Kartoffel/BareDuino/Nano/pictures/IMG_1930.jpg

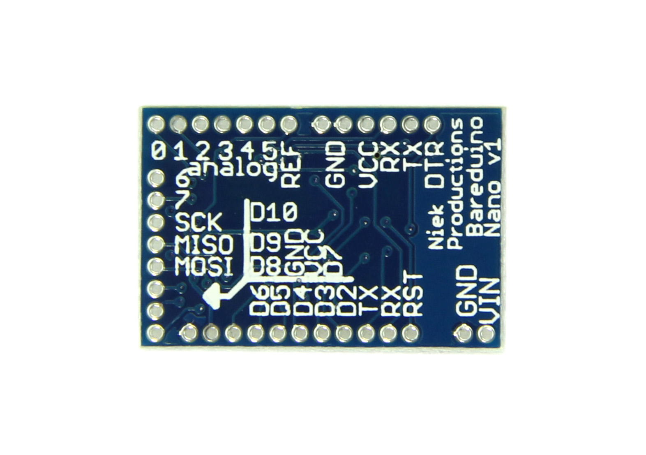
Nano/pictures/IMG_1930.jpg
